joyfulnoisesynth/JNTUB/firmware/LFO/Tables.h

/*
  Copyright (C) 2021  Ben Reeves

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
  ==============================================================================

  Project:     JoyfulNoise LFO
  File:        Tables.h
  Description: Wavetables

 */

#include <avr/pgmspace.h>
#include <stdint.h>

const int8_t WT_SINE[256] PROGMEM = {
  0,  // 0
  3,  // 1
  6,  // 2
  9,  // 3
  12,  // 4
  15,  // 5
  18,  // 6
  21,  // 7
  24,  // 8
  27,  // 9
  30,  // 10
  34,  // 11
  37,  // 12
  39,  // 13
  42,  // 14
  45,  // 15
  48,  // 16
  51,  // 17
  54,  // 18
  57,  // 19
  60,  // 20
  62,  // 21
  65,  // 22
  68,  // 23
  70,  // 24
  73,  // 25
  75,  // 26
  78,  // 27
  80,  // 28
  83,  // 29
  85,  // 30
  87,  // 31
  90,  // 32
  92,  // 33
  94,  // 34
  96,  // 35
  98,  // 36
  100,  // 37
  102,  // 38
  104,  // 39
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
};

const int8_t WT_TRIANGLE[256] PROGMEM = {
  0,  //0
  1,  //1
  3,  //2
  5,  //3
  7,  //4
  9,  //5
  11,  //6
  13,  //7
  15,  //8
  17,  //9
  19,  //10
  21,  //11
  23,  //12
  25,  //13
  27,  //14
  29,  //15
  31,  //16
  33,  //17
  35,  //18
  37,  //19
  39,  //20
  41,  //21
  43,  //22
  45,  //23
  47,  //24
  49,  //25
  51,  //26
  53,  //27
  55,  //28
  57,  //29
  59,  //30
  61,  //31
  63,  //32
  65,  //33
  67,  //34
  69,  //35
  71,  //36
  73,  //37
  75,  //38
  77,  //39
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
};

const int8_t WT_SAWTOOTH[256] PROGMEM = {
  127,  // 0
  126,  // 1
  125,  // 2
  124,  // 3
  123,  // 4
  122,  // 5
  121,  // 6
  120,  // 7
  119,  // 8
  118,  // 9
  117,  // 10
  116,  // 11
  115,  // 12
  114,  // 13
  113,  // 14
  112,  // 15
  111,  // 16
  110,  // 17
  109,  // 18
  108,  // 19
  107,  // 20
  106,  // 21
  105,  // 22
  104,  // 23
  103,  // 24
  102,  // 25
  101,  // 26
  100,  // 27
  99,  // 28
  98,  // 29
  97,  // 30
  96,  // 31
  95,  // 32
  94,  // 33
  93,  // 34
  92,  // 35
  91,  // 36
  90,  // 37
  89,  // 38
  88,  // 39
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
};

const int8_t WT_SQUARE[256] PROGMEM = {
  127,  // 0
  127,  // 1
  127,  // 2
  127,  // 3
  127,  // 4
  127,  // 5
  127,  // 6
  127,  // 7
  127,  // 8
  127,  // 9
  127,  // 10
  127,  // 11
  127,  // 12
  127,  // 13
  127,  // 14
  127,  // 15
  127,  // 16
  127,  // 17
  127,  // 18
  127,  // 19
  127,  // 20
  127,  // 21
  127,  // 22
  127,  // 23
  127,  // 24
  127,  // 25
  127,  // 26
  127,  // 27
  127,  // 28
  127,  // 29
  127,  // 30
  127,  // 31
  127,  // 32
  127,  // 33
  127,  // 34
  127,  // 35
  127,  // 36
  127,  // 37
  127,  // 38
  127,  // 39
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
};

const int8_t WT_RAMP[256] PROGMEM = {
  -128,  // 0
  -127,  // 1
  -126,  // 2
  -125,  // 3
  -124,  // 4
  -123,  // 5
  -122,  // 6
  -121,  // 7
  -120,  // 8
  -119,  // 9
  -118,  // 10
  -117,  // 11
  -116,  // 12
  -115,  // 13
  -114,  // 14
  -113,  // 15
  -112,  // 16
  -111,  // 17
  -110,  // 18
  -109,  // 19
  -108,  // 20
  -107,  // 21
  -106,  // 22
  -105,  // 23
  -104,  // 24
  -103,  // 25
  -102,  // 26
  -101,  // 27
  -100,  // 28
  -99,  // 29
  -98,  // 30
  -97,  // 31
  -96,  // 32
  -95,  // 33
  -94,  // 34
  -93,  // 35
  -92,  // 36
  -91,  // 37
  -90,  // 38
  -89,  // 39
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
};
