joyfulnoisesynth/JNTUB/firmware/D-VCO/Tables.h

/*
  Copyright (C) 2021  Ben Reeves

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
  ==============================================================================

  Project:     JoyfulNoise D-VCO
  File:        Tables.h
  Description: Wavetables and other static data

 */

#include <avr/pgmspace.h>
#include <stdint.h>

/**
 * Sample rate is 20 kHz, and phase increments from 0 to 65535 in increments
 * of Pitch units every sample. This gives us the relation:
 *
 *   Frequency = (20,000 * Pitch) / 65535
 *                   or
 *       Pitch = Frequency * 65535 / 20,000
 *
 * This table defines this function for MIDI notes 0 to 127.
 */
const uint16_t MIDI_NOTE_PITCHES[128] PROGMEM = {
  // MIDI 0 - (ideal: 8.18 Hz) (actual: 7.93) (error: 52 cents)
  26,
  // MIDI 1 - (ideal: 8.66 Hz) (actual: 8.54) (error: 23 cents)
  28,
  // MIDI 2 - (ideal: 9.18 Hz) (actual: 9.16) (error: 4 cents)
  30,
  // MIDI 3 - (ideal: 9.72 Hz) (actual: 9.46) (error: 46 cents)
  31,
  // MIDI 4 - (ideal: 10.30 Hz) (actual: 10.07) (error: 38 cents)
  33,
  // MIDI 5 - (ideal: 10.91 Hz) (actual: 10.68) (error: 36 cents)
  35,
  // MIDI 6 - (ideal: 11.56 Hz) (actual: 11.29) (error: 40 cents)
  37,
  // MIDI 7 - (ideal: 12.25 Hz) (actual: 12.21) (error: 6 cents)
  40,
  // MIDI 8 - (ideal: 12.98 Hz) (actual: 12.82) (error: 21 cents)
  42,
  // MIDI 9 - (ideal: 13.75 Hz) (actual: 13.73) (error: 2 cents)
  45,
  // MIDI 10 - (ideal: 14.57 Hz) (actual: 14.34) (error: 27 cents)
  47,
  // MIDI 11 - (ideal: 15.43 Hz) (actual: 15.26) (error: 19 cents)
  50,
  // MIDI 12 - (ideal: 16.35 Hz) (actual: 16.17) (error: 18 cents)
  53,
  // MIDI 13 - (ideal: 17.32 Hz) (actual: 17.09) (error: 23 cents)
  56,
  // MIDI 14 - (ideal: 18.35 Hz) (actual: 18.31) (error: 3 cents)
  60,
  // MIDI 15 - (ideal: 19.45 Hz) (actual: 19.23) (error: 20 cents)
  63,
  // MIDI 16 - (ideal: 20.60 Hz) (actual: 20.45) (error: 12 cents)
  67,
  // MIDI 17 - (ideal: 21.83 Hz) (actual: 21.67) (error: 12 cents)
  71,
  // MIDI 18 - (ideal: 23.12 Hz) (actual: 22.89) (error: 17 cents)
  75,
  // MIDI 19 - (ideal: 24.50 Hz) (actual: 24.41) (error: 6 cents)
  80,
  // MIDI 20 - (ideal: 25.96 Hz) (actual: 25.94) (error: 1 cents)
  85,
  // MIDI 21 - A0  (ideal: 27.50 Hz) (actual: 27.47) (error: 2 cents)
  90,
  // MIDI 22 - A#0 (ideal: 29.14 Hz) (actual: 28.99) (error: 8 cents)
  95,
  // MIDI 23 - B0  (ideal: 30.87 Hz) (actual: 30.82) (error: 2 cents)
  101,
  // MIDI 24 - C1  (ideal: 32.70 Hz) (actual: 32.65) (error: 2 cents)
  107,
  // MIDI 25 - C#1 (ideal: 34.65 Hz) (actual: 34.48) (error: 8 cents)
  113,
  // MIDI 26 - D1  (ideal: 36.71 Hz) (actual: 36.62) (error: 4 cents)
  120,
  // MIDI 27 - D#1 (ideal: 38.89 Hz) (actual: 38.76) (error: 5 cents)
  127,
  // MIDI 28 - E1  (ideal: 41.20 Hz) (actual: 41.20) (error: 0 cents)
  135,
  // MIDI 29 - F1  (ideal: 43.65 Hz) (actual: 43.64) (error: 0 cents)
  143,
  // MIDI 30 - F#1 (ideal: 46.25 Hz) (actual: 46.08) (error: 6 cents)
  151,
  // MIDI 31 - G1  (ideal: 49.00 Hz) (actual: 48.83) (error: 6 cents)
  160,
  // MIDI 32 - G#1 (ideal: 51.91 Hz) (actual: 51.88) (error: 1 cents)
  170,
  // MIDI 33 - A1  (ideal: 55.00 Hz) (actual: 54.93) (error: 2 cents)
  180,
  // MIDI 34 - A#1 (ideal: 58.27 Hz) (actual: 57.98) (error: 8 cents)
  190,
  // MIDI 35 - B1  (ideal: 61.74 Hz) (actual: 61.65) (error: 2 cents)
  202,
  // MIDI 36 - C2  (ideal: 65.41 Hz) (actual: 65.31) (error: 2 cents)
  214,
  // MIDI 37 - C#2 (ideal: 69.30 Hz) (actual: 69.27) (error: 0 cents)
  227,
  // MIDI 38 - D2  (ideal: 73.42 Hz) (actual: 73.24) (error: 4 cents)
  240,
  // MIDI 39 - D#2 (ideal: 77.78 Hz) (actual: 77.51) (error: 5 cents)
  254,
  // MIDI 40 - E2  (ideal: 82.41 Hz) (actual: 82.40) (error: 0 cents)
  270,
  // MIDI 41 - F2  (ideal: 87.31 Hz) (actual: 87.28) (error: 0 cents)
  286,
  // MIDI 42 - F#2 (ideal: 92.50 Hz) (actual: 92.47) (error: 0 cents)
  303,
  // MIDI 43 - G2  (ideal: 98.00 Hz) (actual: 97.96) (error: 0 cents)
  321,
  // MIDI 44 - G#2 (ideal: 103.83 Hz) (actual: 103.76) (error: 1 cents)
  340,
  // MIDI 45 - A2  (ideal: 110.00 Hz) (actual: 109.86) (error: 2 cents)
  360,
  // MIDI 46 - A#2 (ideal: 116.54 Hz) (actual: 116.27) (error: 3 cents)
  381,
  // MIDI 47 - B2  (ideal: 123.47 Hz) (actual: 123.29) (error: 2 cents)
  404,
  // MIDI 48 - C3  (ideal: 130.81 Hz) (actual: 130.62) (error: 2 cents)
  428,
  // MIDI 49 - C#3 (ideal: 138.59 Hz) (actual: 138.55) (error: 0 cents)
  454,
  // MIDI 50 - D3  (ideal: 146.83 Hz) (actual: 146.79) (error: 0 cents)
  481,
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
  -108,  //19
  -107,  //20
  -106,  //21
  -105,  //22
  -104,  //23
  -103,  //24
  -102,  //25
  -101,  //26
  -100,  //27
  -99,  //28
  -98,  //29
  -97,  //30
  -96,  //31
  -95,  //32
  -94,  //33
  -93,  //34
  -92,  //35
  -91,  //36
  -90,  //37
  -89,  //38
  -88,  //39
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
};
